aki27kbd/cocot36plus/images/IMG_1310.JPEG

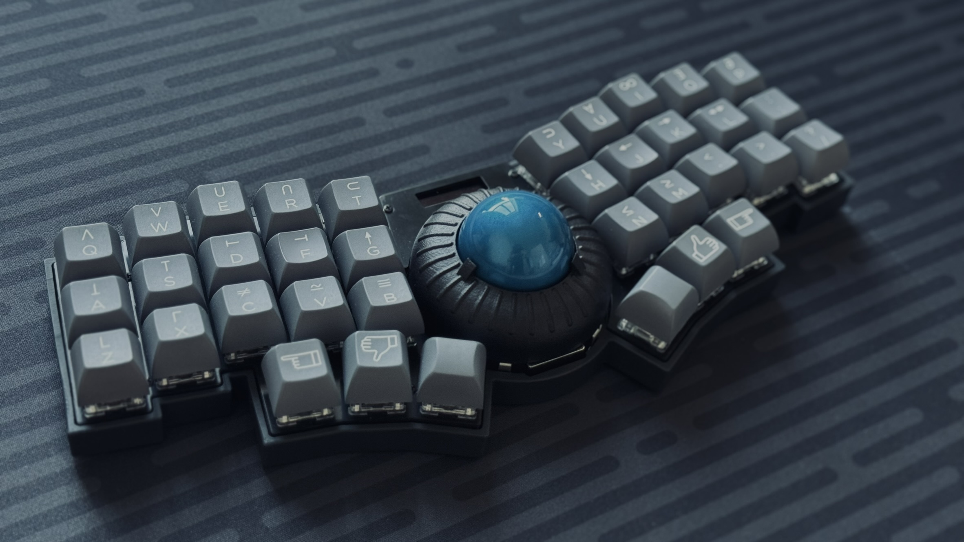
images/IMG_1310.JPEG
