aki27kbd/cocot36plus/images/IMG_1312.JPEG

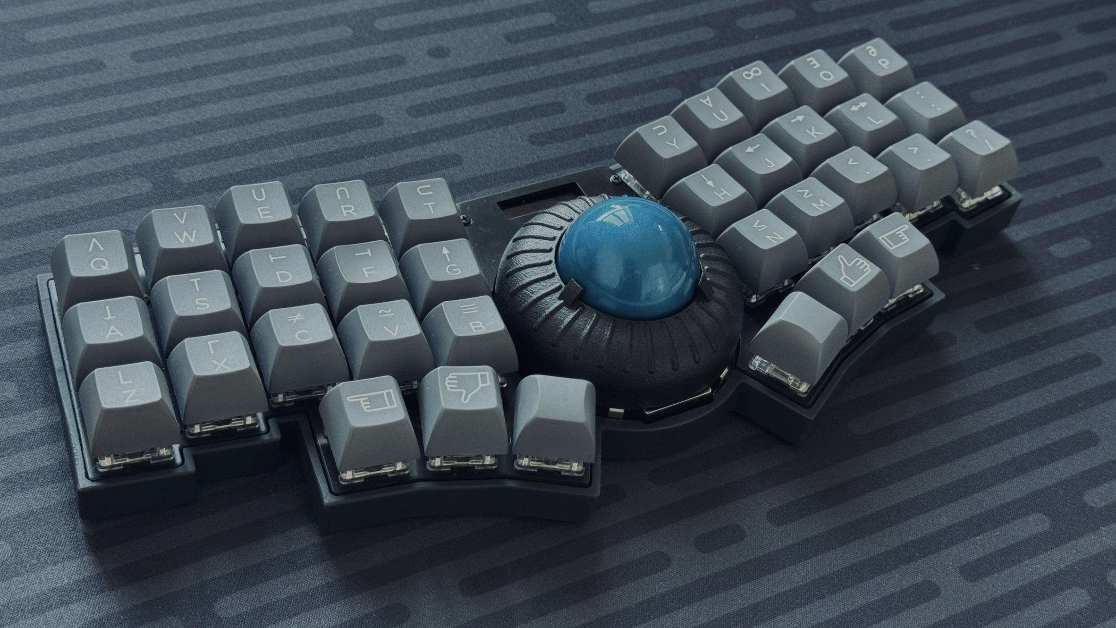
images/IMG_1312.JPEG
