aki27kbd/cocot36plus/images/IMG_1313.JPEG

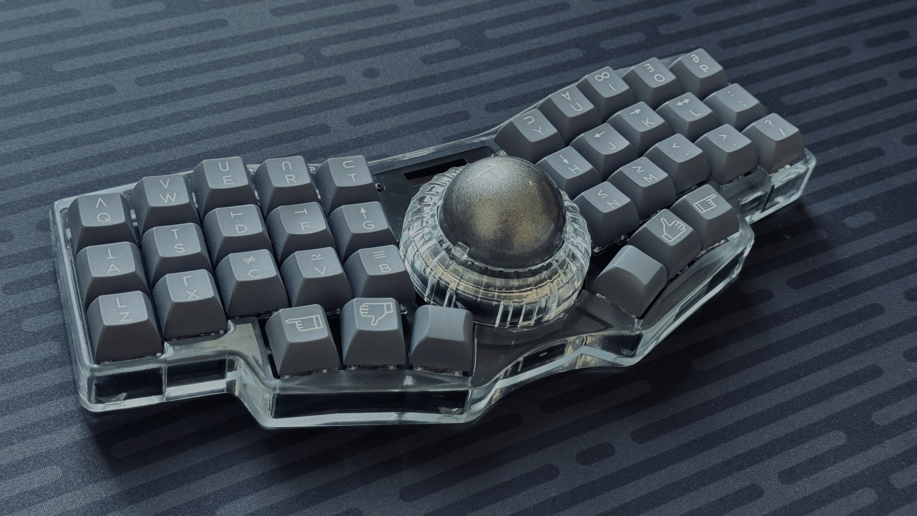
images/IMG_1313.JPEG
