aki27kbd/cocot36plus/v1/images/bg_00.jpg

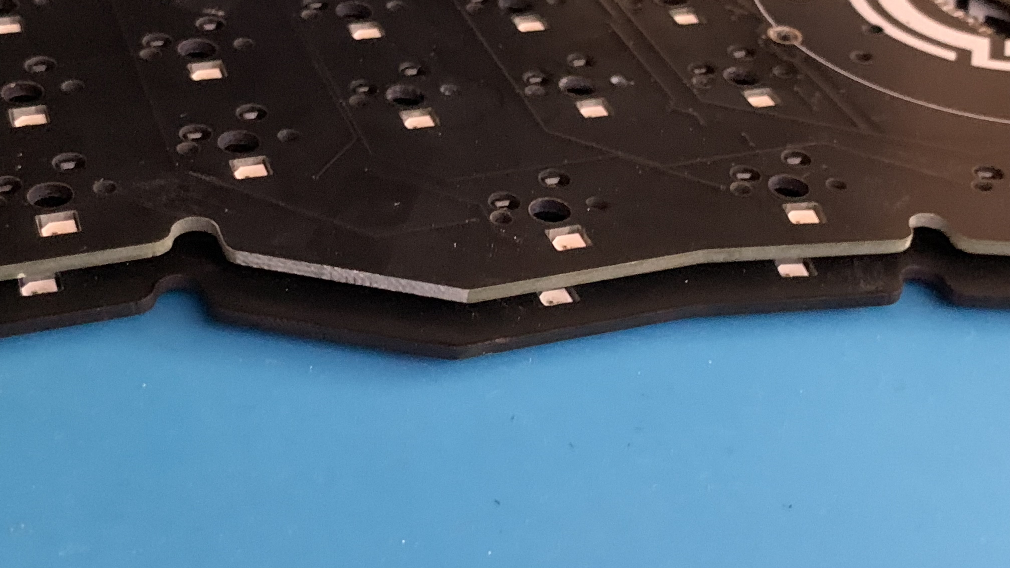
v1/images/bg_00.jpg
