aki27kbd/cocot36plus/v1/images/main_01.jpg

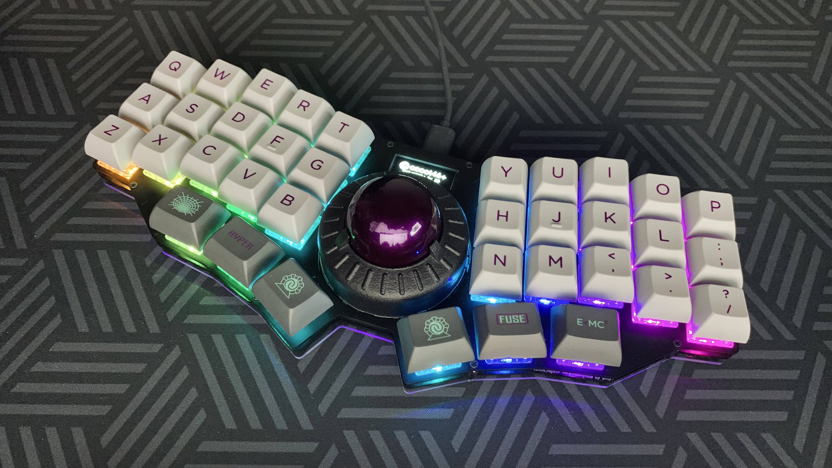
v1/images/main_01.jpg
